karskiliini/64korppu/tools/render-3d.py

#!/usr/bin/env python3
"""
Render 3D-style visualization of PCB variants with components.
Shows top view and isometric perspective with component bodies.

Renders both 2-layer and 4-layer variants.
"""
import matplotlib.pyplot as plt
import matplotlib.patches as patches
from matplotlib.patches import FancyBboxPatch
import numpy as np


# ── Board configs ──────────────────────────────────────────────────────

BOARDS = {
    '4-layer': {
        'title': '64korppu-E — 4-Layer PCB',
        'output': 'hardware/E-IEC-Nano-SRAM/4-layer/64korppu-E-4layer-3d.png',
        'board': (100, 100, 170, 160),  # x1, y1, x2, y2
        'layers': '4-layer: F.Cu / GND / +5V / B.Cu',
        'components': [
            # Mounting holes
            ('H1', 101, 101, 105, 105, '', '#888888', 0),
            ('H2', 165, 101, 169, 105, '', '#888888', 0),
            ('H3', 101, 155, 105, 159, '', '#888888', 0),
            ('H4', 165, 155, 169, 159, '', '#888888', 0),
            # Power
            ('J3', 106, 100.5, 120, 113, 'DC 5V', '#2a2a2a', 11),
            ('C4', 124, 101.5, 129, 106.5, '10µF', '#CD853F', 8),
            ('D1', 130, 102, 134, 106, 'LED', '#00CC00', 5),
            ('R8', 135.5, 102.5, 148.5, 105.5, '330Ω', '#DEB887', 2.5),
            # IEC series resistors
            ('R1', 106.5, 114.5, 119.5, 117.5, '1kΩ', '#DEB887', 2.5),
            ('R2', 106.5, 118.5, 119.5, 121.5, '1kΩ', '#DEB887', 2.5),
            ('R3', 106.5, 122.5, 119.5, 125.5, '1kΩ', '#DEB887', 2.5),
            ('R4', 106.5, 126.5, 119.5, 129.5, '1kΩ', '#DEB887', 2.5),
            # IEC pull-up resistors
            ('R5', 106.5, 130.5, 119.5, 133.5, '4.7kΩ', '#DEB887', 2.5),
            ('R6', 106.5, 134.5, 119.5, 137.5, '4.7kΩ', '#DEB887', 2.5),
            ('R7', 106.5, 138.5, 119.5, 141.5, '4.7kΩ', '#DEB887', 2.5),
            # DIN-6 IEC connector
            ('J1', 106, 143, 122, 159, 'IEC\nDIN-6', '#333333', 15),
            # Arduino Nano
            ('U1', 133, 109.5, 140, 147.5, 'Arduino\nNano', '#0066CC', 10),
            # Floppy pull-up resistors
            ('R9',  146.5, 106.5, 159.5, 109.5, '10kΩ', '#DEB887', 2.5),
            ('R10', 146.5, 111.5, 159.5, 114.5, '10kΩ', '#DEB887', 2.5),
            ('R11', 146.5, 116.5, 159.5, 119.5, '10kΩ', '#DEB887', 2.5),
            ('R12', 146.5, 121.5, 159.5, 124.5, '10kΩ', '#DEB887', 2.5),
            # Floppy IDC connector
            ('J2', 160.5, 108, 169.5, 152, 'Floppy\nIDC\n2x17', '#444444', 10),
            # SRAM DIP-8
            ('U2', 123.5, 148.5, 134, 159, 'SRAM\n23LC256', '#333333', 5),
            # 74HC595 DIP-16
            ('U3', 146.5, 130.5, 157, 152, '74HC595', '#333333', 5),
            # Bypass caps
            ('C1', 135, 148.5, 142, 153.5, '100nF', '#CD853F', 3),
            ('C2', 135, 154.5, 142, 159.5, '100nF', '#CD853F', 3),
            ('C3', 147, 153.5, 154, 158.5, '100nF', '#CD853F', 3),
        ],
        'test_points': [
            ('TP1',  103, 108.0, 'GND'),
            ('TP2',  103, 110.5, '+5V'),
            ('TP3',  103, 113.0, 'ATN'),
            ('TP4',  103, 115.5, 'CLK'),
            ('TP5',  103, 118.0, 'DATA'),
            ('TP6',  103, 120.5, 'MOTOR'),
            ('TP7',  103, 123.0, 'STEP'),
            ('TP8',  103, 125.5, 'RDATA'),
            ('TP9',  103, 128.0, 'WDATA'),
            ('TP10', 103, 130.5, 'SIDE1'),
            ('TP11', 103, 133.0, 'SCK'),
            ('TP12', 103, 135.5, 'MOSI'),
            ('TP13', 103, 138.0, 'MISO'),
            ('TP14', 103, 140.5, 'CS'),
        ],
    },
    '2-layer': {
        'title': '64korppu-E — 2-Layer PCB',
        'output': 'hardware/E-IEC-Nano-SRAM/2-layer/64korppu-E-2layer-3d.png',
        'board': (100, 100, 240, 220),  # 140x120mm
        'layers': '2-layer: F.Cu / B.Cu',
        'components': [
            # Mounting holes
            ('H1', 101, 101, 105, 105, '', '#888888', 0),
            ('H2', 235, 101, 239, 105, '', '#888888', 0),
            ('H3', 101, 215, 105, 219, '', '#888888', 0),
            ('H4', 235, 215, 239, 219, '', '#888888', 0),
            # Power
            ('J3', 157, 103.5, 171, 116, 'DC 5V', '#2a2a2a', 11),
            ('C4', 179, 105.5, 184, 110.5, '10µF', '#CD853F', 8),
            # IEC series resistors
            ('R1', 120.5, 120.5, 133.5, 123.5, '1kΩ', '#DEB887', 2.5),
            ('R2', 120.5, 127.5, 133.5, 130.5, '1kΩ', '#DEB887', 2.5),
            ('R3', 120.5, 134.5, 133.5, 137.5, '1kΩ', '#DEB887', 2.5),
            ('R4', 120.5, 141.5, 133.5, 144.5, '1kΩ', '#DEB887', 2.5),
            # IEC pull-up resistors
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
